pulsatrix-emobility/CP-PP-miniEVsimulator/CP-PP-miniEVsimulator.sch

## KiCad design CP-PP-miniEVsimulator.sch (2021-09-16)

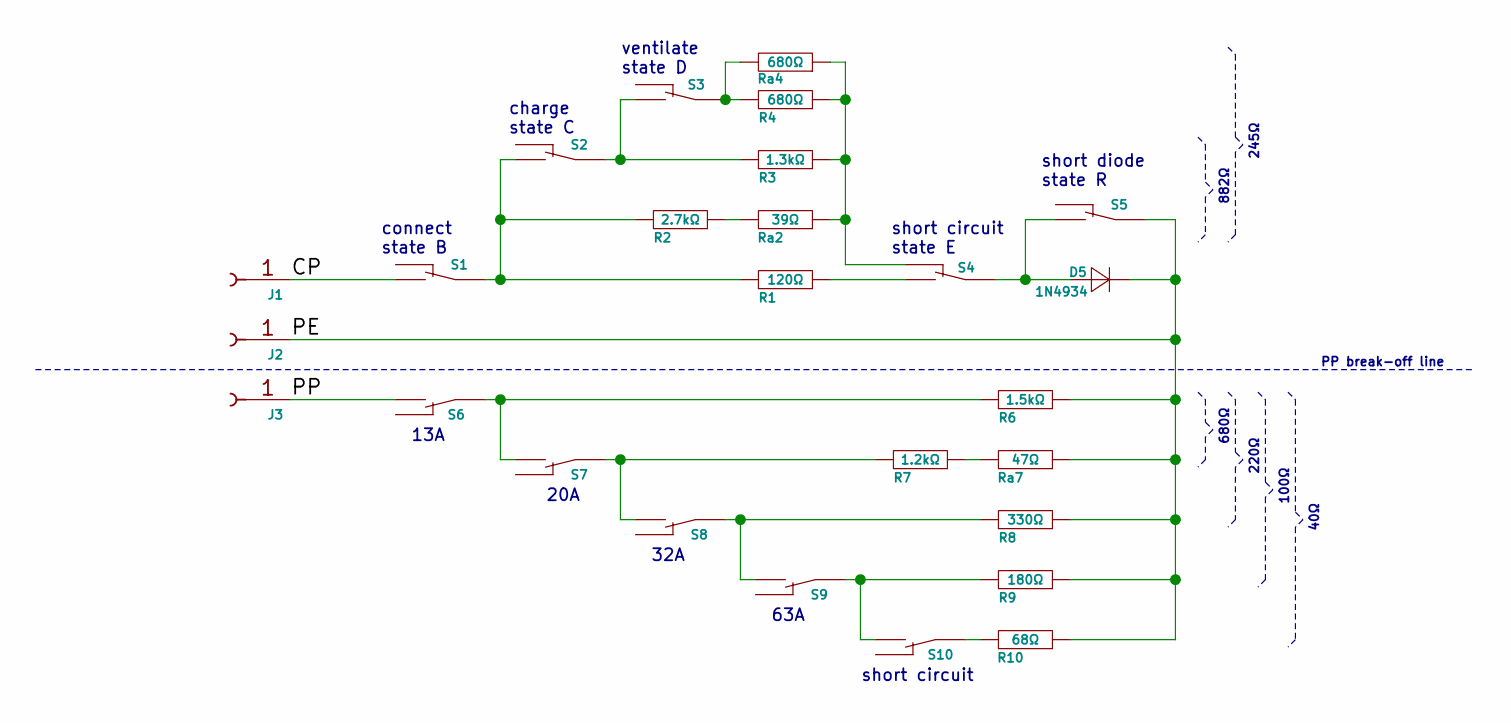
[picture p7: schematic CP-PP-miniEVsimulator.sch]

Parts:
D5: 1N4934; D_A-405_P7.62mm_Horizontal; LCSC C146704
J1, J2, J3: Conn_01x01_Female; SolderWire-0.25sqmm_1x01_D0.65mm_OD2mm_Relief
R1: 120Ω; R_Axial_DIN0207_L6.3mm_D2.5mm_P7.62mm_Horizontal; LCSC C58619
R2: 2.7kΩ; R_Axial_DIN0207_L6.3mm_D2.5mm_P7.62mm_Horizontal; LCSC C58615
R3: 1.3kΩ; R_Axial_DIN0207_L6.3mm_D2.5mm_P7.62mm_Horizontal; LCSC C337167
R4: 680Ω; R_Axial_DIN0207_L6.3mm_D2.5mm_P7.62mm_Horizontal; LCSC C58599
R6: 1.5kΩ; R_Axial_DIN0207_L6.3mm_D2.5mm_P7.62mm_Horizontal; LCSC C58620
R7: 1.2kΩ; R_Axial_DIN0207_L6.3mm_D2.5mm_P7.62mm_Horizontal; LCSC C58590
R8: 330Ω; R_Axial_DIN0207_L6.3mm_D2.5mm_P7.62mm_Horizontal; LCSC C58608
R9: 180Ω; R_Axial_DIN0207_L6.3mm_D2.5mm_P7.62mm_Horizontal; LCSC C58665
R10: 68Ω; R_Axial_DIN0207_L6.3mm_D2.5mm_P7.62mm_Horizontal; LCSC C58629
Ra2: 39Ω; R_Axial_DIN0207_L6.3mm_D2.5mm_P7.62mm_Horizontal; LCSC C58644
Ra4: 680Ω; R_Axial_DIN0207_L6.3mm_D2.5mm_P7.62mm_Horizontal; LCSC C58599
Ra7: 47Ω; R_Axial_DIN0207_L6.3mm_D2.5mm_P7.62mm_Horizontal; LCSC C58604
S1, S2, S3, S4, S5, S6, S7, S8, S9, S10: Switch_SPDT; miniatureToggleSwitch_12.7x6.6; LCSC C312276

Connections:
CP: J1.1, S1.2 (NO)
unnamed: D5.2 (A), S4.1 (COM), S5.2 (NO)
unnamed: R1.1, S4.2 (NO)
unnamed: R1.2, R2.2, S1.1 (COM), S2.2 (NO)
unnamed: R2.1, Ra2.2
unnamed: R3.1, R4.1, Ra2.1, Ra4.1, S4.3 (NC)
unnamed: R3.2, S2.1 (COM), S3.2 (NO)
unnamed: R4.2, Ra4.2, S3.1 (COM)
unnamed: R6.2, S6.1 (COM), S7.2 (NO)
unnamed: R7.1, Ra7.2
unnamed: R7.2, S7.1 (COM), S8.2 (NO)
unnamed: R8.2, S8.1 (COM), S9.2 (NO)
unnamed: R9.2, S9.1 (COM), S10.2 (NO)
unnamed: R10.2, S10.1 (COM)
PE: D5.1 (K), J2.1, R6.1, R8.1, R9.1, R10.1, Ra7.1, S5.1 (COM)
PP: J3.1, S6.2 (NO)

Notes on the sheet:
short diode state R
short circuit state E
100Ω
40Ω
PP break-off line
short circuit
63A
32A
20A
13A
ventilate state D
charge state C
connect state B
882Ω
220Ω
680Ω
245Ω
